merlinkv/Omega_MSX2/Mainboard_1_1_MKV/OmegaMB_1_1_MKV_Back.jpg

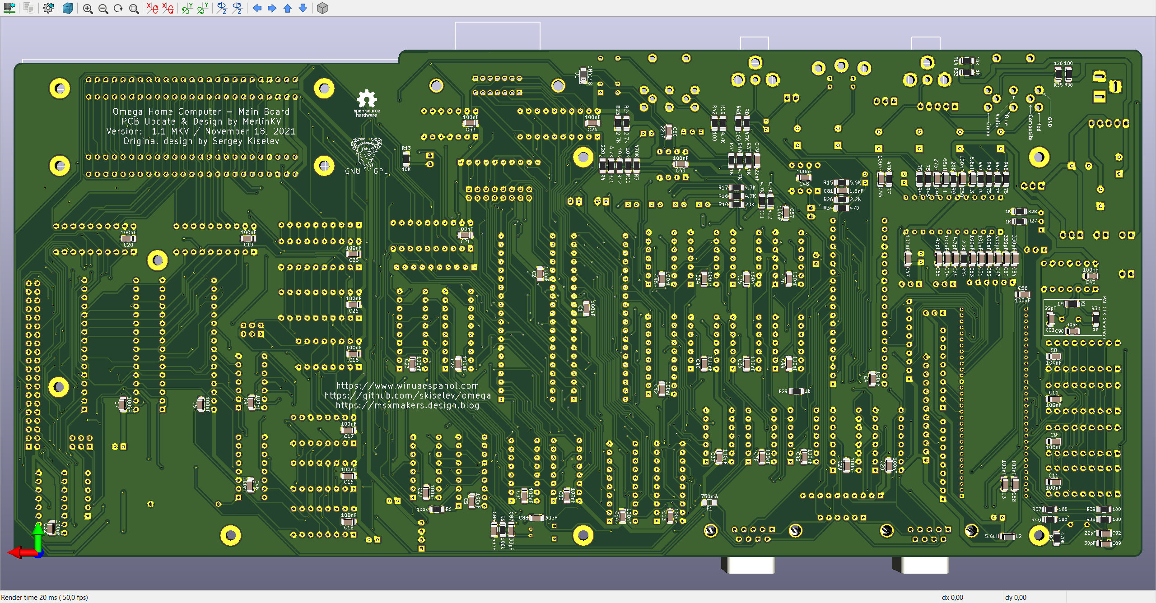
Mainboard_1_1_MKV/OmegaMB_1_1_MKV_Back.jpg
