merlinkv/Omega_MSX2/Mainboard_1_2_5_MKV/OmegaMB_1_2_5_MKV_Back.jpg

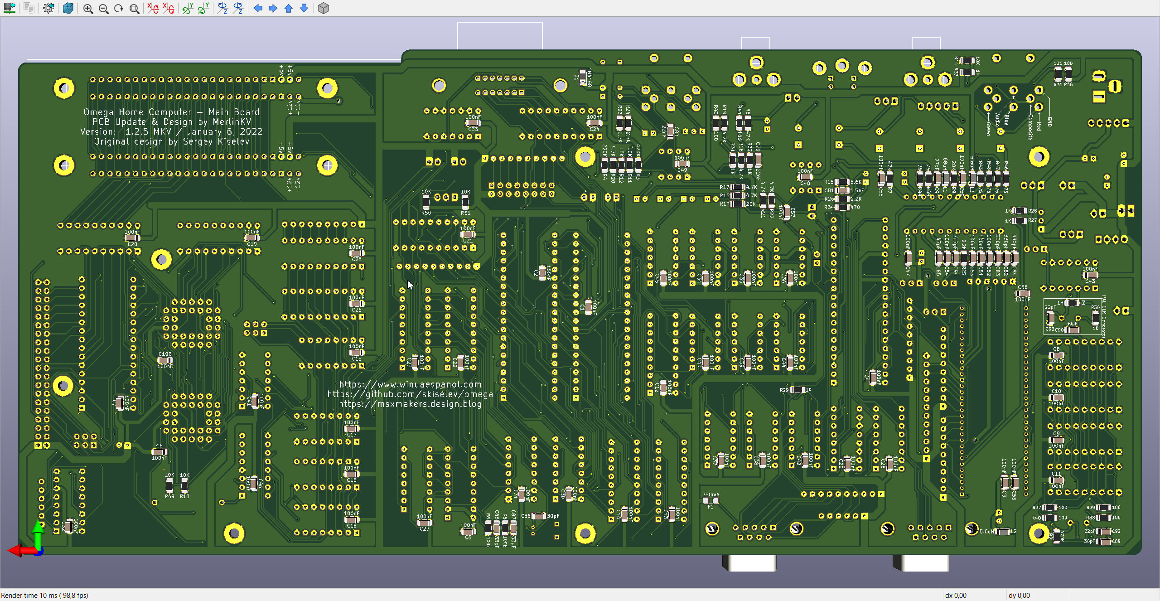
Mainboard_1_2_5_MKV/OmegaMB_1_2_5_MKV_Back.jpg
