merlinkv/Omega_MSX2/Mainboard_1_2_MKV/OmegaMB_1_2_MKV_Back.jpg

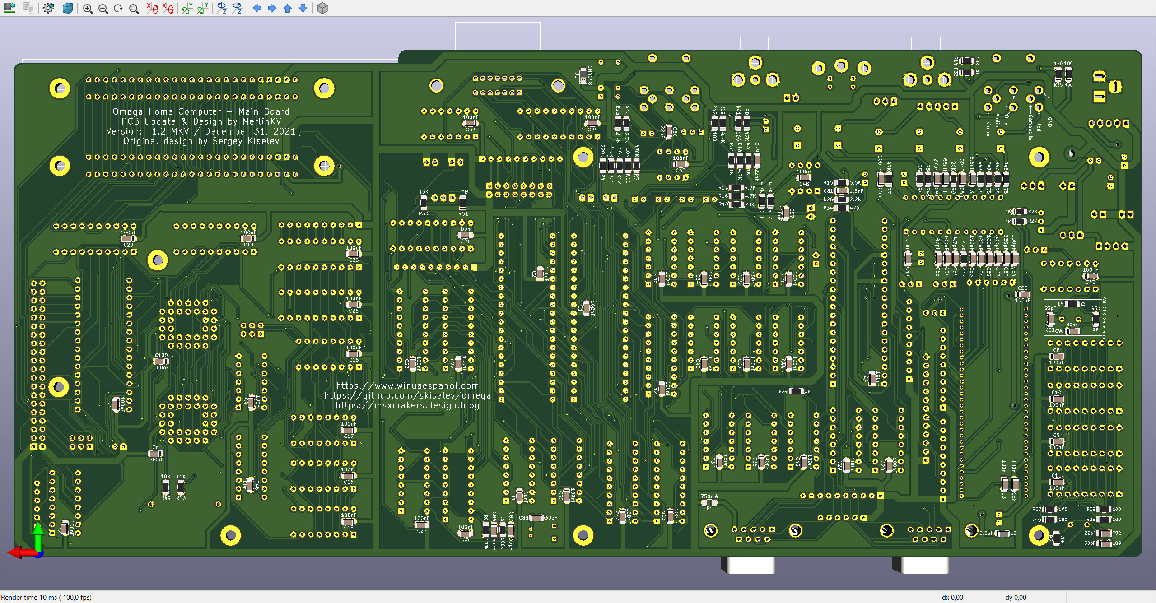
Mainboard_1_2_MKV/OmegaMB_1_2_MKV_Back.jpg
